reubenwbetts/Digitally-Controlled-Analog-EQ/Digital-Control/Digipot-Board/PCB-Layouts/Layer 1 (top).png

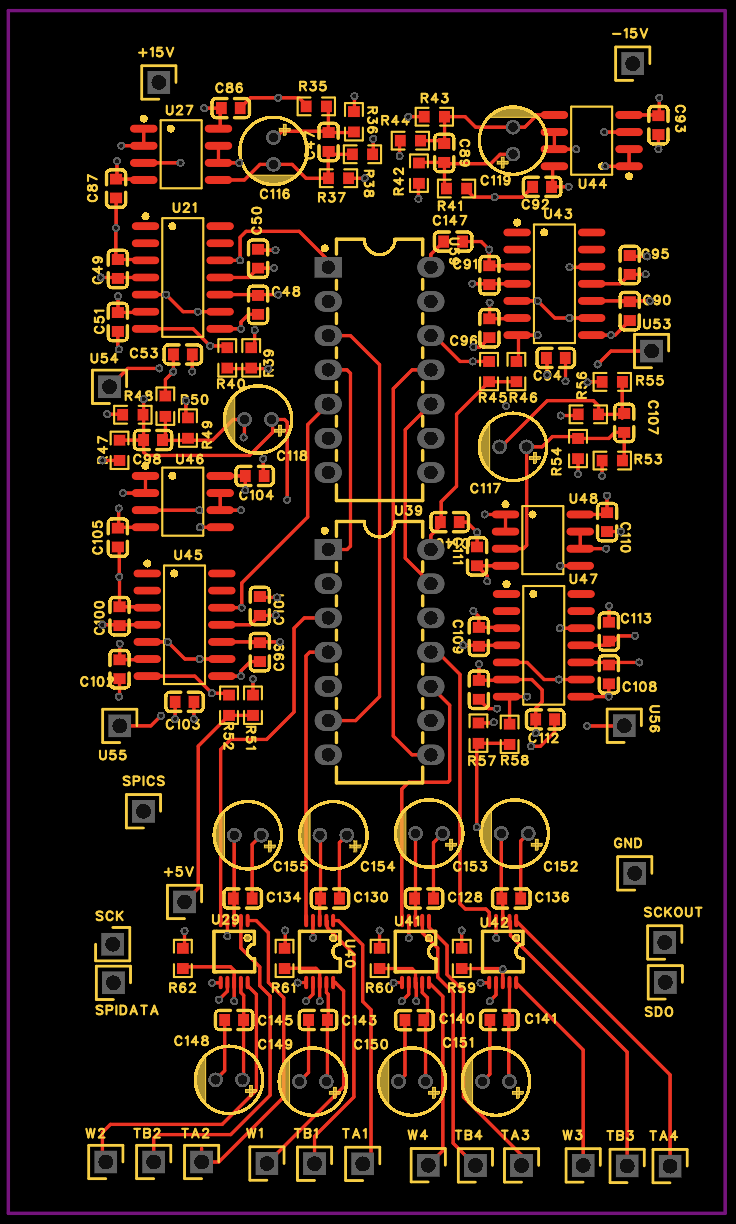
Digital-Control/Digipot-Board/PCB-Layouts/Layer 1 (top).png
