reubenwbetts/Digitally-Controlled-Analog-EQ/Digital-Control/Digipot-Board/PCB-Layouts/Layer 2.png

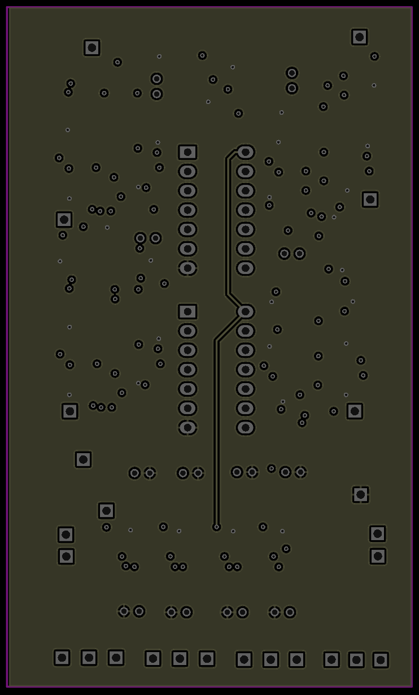
Digital-Control/Digipot-Board/PCB-Layouts/Layer 2.png
