reubenwbetts/Digitally-Controlled-Analog-EQ/Digital-Control/Digipot-Board/PCB-Layouts/Layer 3.png

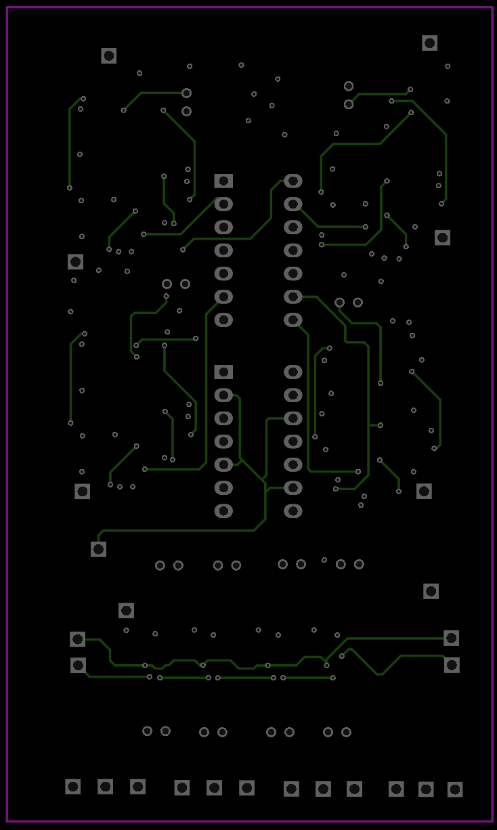
Digital-Control/Digipot-Board/PCB-Layouts/Layer 3.png
