reubenwbetts/Digitally-Controlled-Analog-EQ/Digital-Control/Digipot-Board/PCB-Layouts/Layer 4 (bottom).png

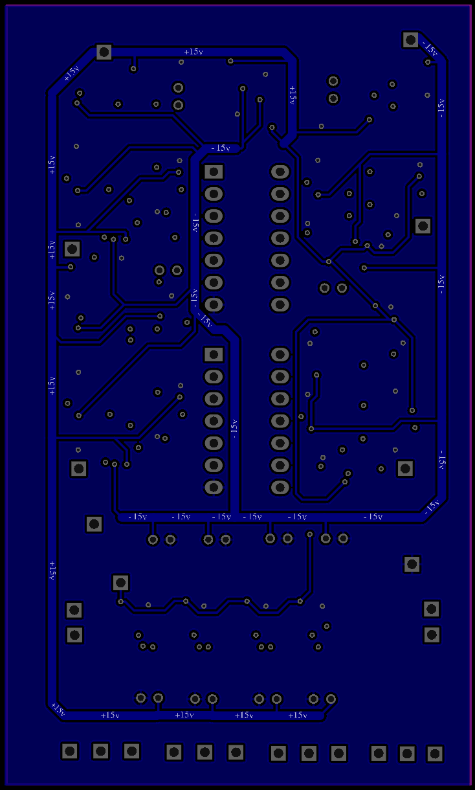
Digital-Control/Digipot-Board/PCB-Layouts/Layer 4 (bottom).png
