reubenwbetts/Digitally-Controlled-Analog-EQ/EQ-Channel/PCB-files/Bottom Layer.png

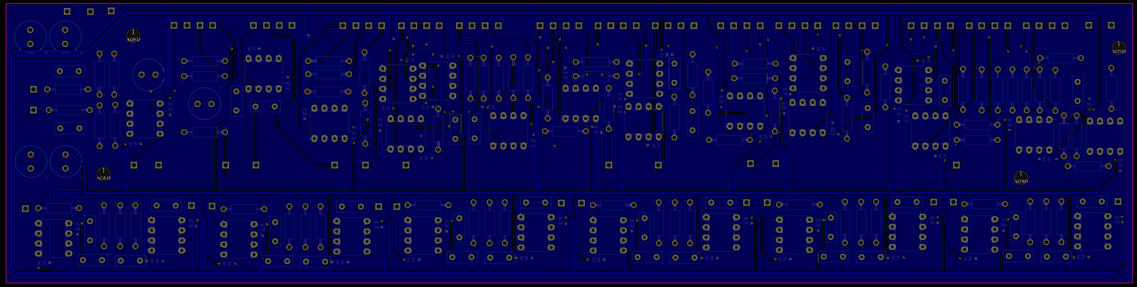
EQ-Channel/PCB-files/Bottom Layer.png
