reubenwbetts/Digitally-Controlled-Analog-EQ/EQ-Channel/PCB-files/Top Layer.png

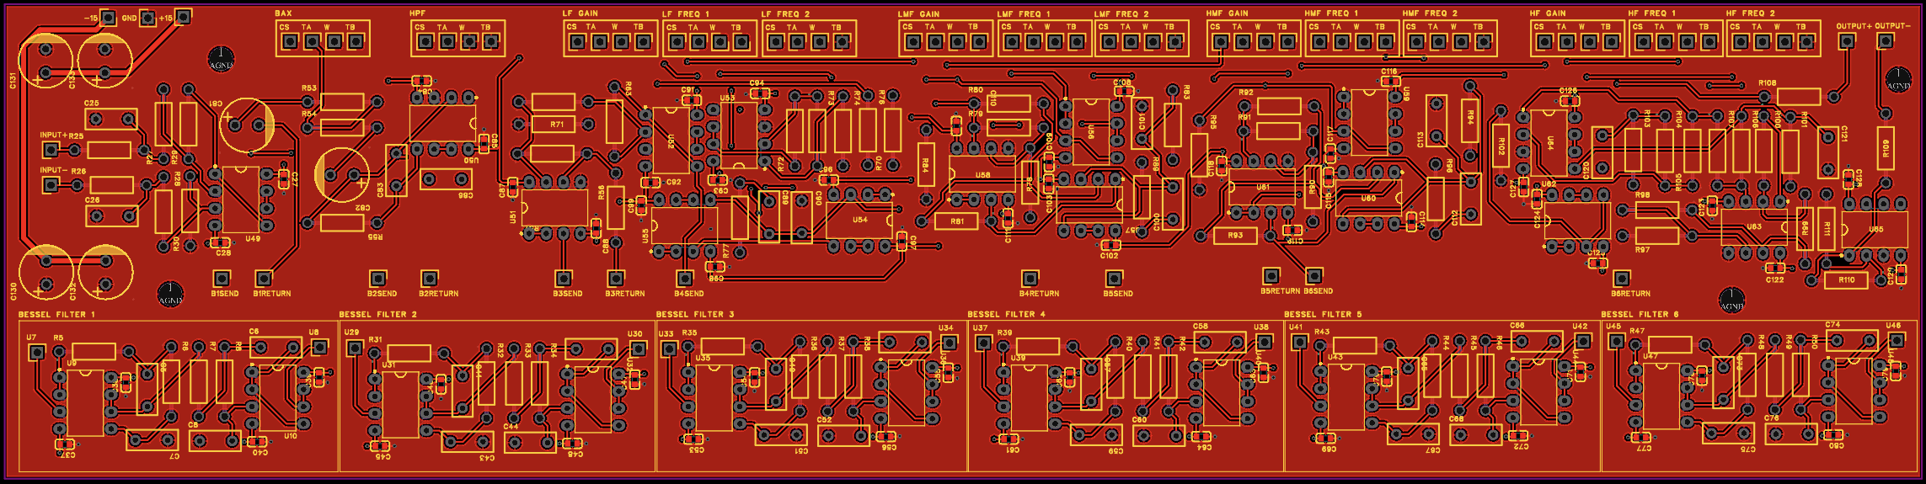
EQ-Channel/PCB-files/Top Layer.png
