reubenwbetts/Digitally-Controlled-Analog-EQ/EQ-Channel/Schematics/Balanced Input.png

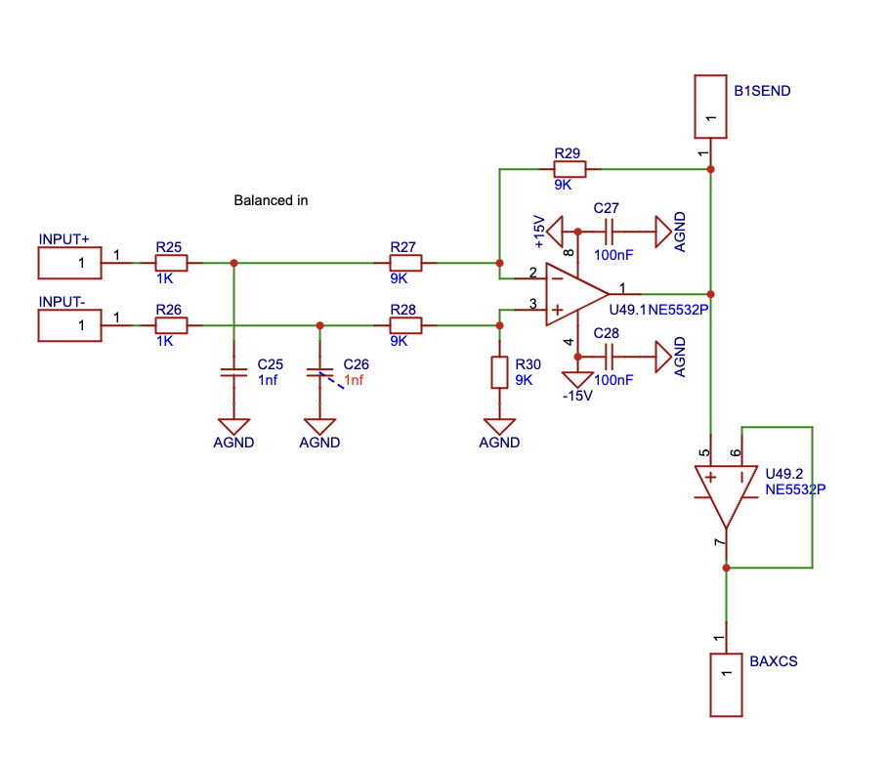
EQ-Channel/Schematics/Balanced Input.png
