reubenwbetts/Digitally-Controlled-Analog-EQ/EQ-Channel/Schematics/Low Mid Bell.png

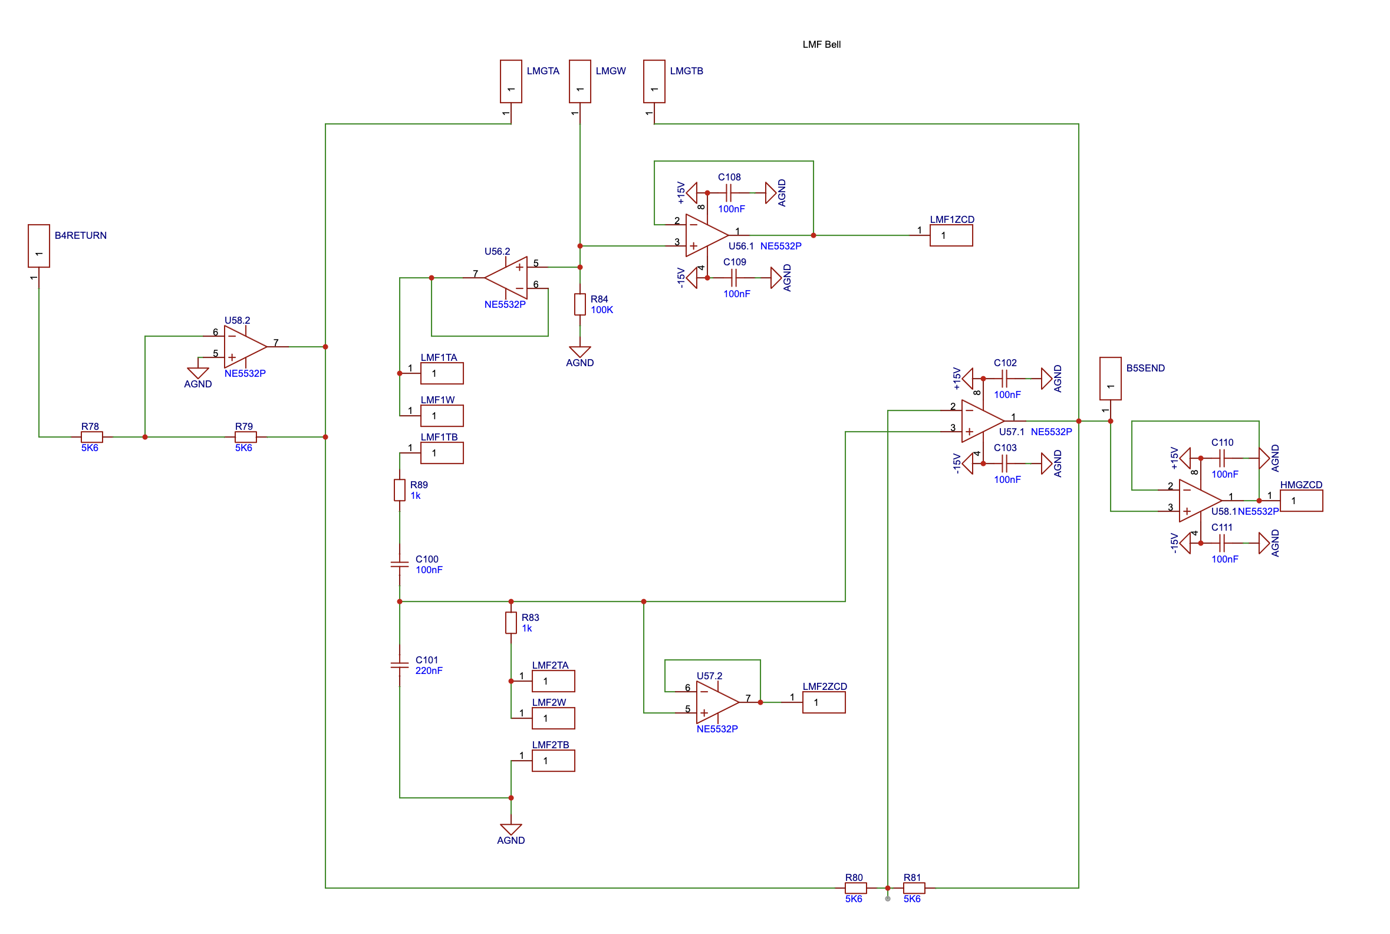
EQ-Channel/Schematics/Low Mid Bell.png
