reubenwbetts/Digitally-Controlled-Analog-EQ/EQ-Channel/Spice-Sims/Balanced Input.asc

C1: cap; 1nf
C2: cap; 1nf
R1: res; 9K
R2: res; 9K
R3: res; 9K
R4: res; 9K
R5: res; 1K
R6: res; 1K
U1: opamp2; NE5532
V1: voltage; 15
V2: voltage; -15
V3: voltage; SINE(0 1 100); AC 1
V4: voltage; SINE(0 1 100 0 0 180); AC 1 180
Named nets: +15, -15, 0, sig-, sig+
.lib LTC.lib
.ac oct 100 1 100k
.tran 0.1
