reubenwbetts/Digitally-Controlled-Analog-EQ/Digital-Control/Bessel-Filter/Spice-Sims/Bessel Filter.asc

0.7381nf: cap; 0.7381nf
C1: cap; 12.0839nf
C2: cap; 9.0713nf
C3: cap; 33nf
C4: cap; 1.5879nf
C5: cap; 0.3791nf
C6: cap; 24nf
C7: cap; 1.3917nf
C8: cap; 0.9403nf
C9: cap; 0.9403nf
C10: cap; 0.7157nf
C11: cap; 1.2772nf
C12: cap; 1.9158nf
C13: cap; 0.9027nf
C14: cap; 0.7157nf
C15: cap; 0.9027nf
C16: cap; 1.0694nf
C17: cap; 720pf
C18: cap; 10pf
C19: cap; 68pf
C20: cap; 540pf
C21: cap; 15pf
C22: cap; 720pf
C23: cap; 10pf
C24: cap; 68pf
C25: cap; 540pf
C26: cap; 15pf
C27: cap; 1.0694nf
C28: cap; 1.5879nf
C29: cap; 0.3791nf
C30: cap; 1.3917nf
C31: cap; 0.7381nf
C32: cap; 1.2772nf
C33: cap; 1.9158nf
R1: res; 220
R2: res; 220
R3: res; 1k
R4: res; 1k
R5: res; 1k
R6: res; 1k
R7: res; 1k
R8: res; 1k
R9: res; 1k
R10: res; 1k
R11: res; 1k
R12: res; 1k
R13: res; 10k
R14: res; 10k
R15: res; 10k
R16: res; 10k
R17: res; 10k
R18: res; 10k
R19: res; 10k
R20: res; 10k
R21: res; 100
R22: res; 100
R23: res; 1k
R24: res; 1k
R25: res; 1k
R26: res; 1k
R27: res; 1k
R28: res; 1k
R29: res; 1k
R30: res; 1k
R31: res; 1k
R32: res; 1k
U1: opamp2; NE5532
U2: opamp2; NE5532
U3: opamp2; NE5532
U4: opamp2; NE5532
U5: opamp2; NE5532
U6: opamp2; NE5532
U7: opamp2; NE5532
U8: opamp2; NE5532
U9: opamp2; NE5532
U10: opamp2; NE5532
U11: opamp2; NE5532
U12: opamp2; NE5532
U13: opamp2; NE5532
U14: opamp2; NE5532
U15: opamp2; NE5532
U16: opamp2; NE5532
V1: voltage; +15
V2: voltage; -15
V3: voltage; SINE(0 1 {sigfreq}); AC 1
Named nets: 0, +15, -15, sig, 6order, 2order, 2ordernewcalc
.lib LTC.lib
.ac oct 100 1 200k
.tran 0 0.0001
2nd Order
voltage sources
simulation directives:
.lib LTC.lib
4th Order
.lib LTC.lib
6th Order
.lib LTC.lib
8th Order
.lib LTC.lib
Components values determined by BesselFilterCalc.m
.lib LTC.lib
2nd Order
.lib LTC.lib
6th Order
.lib LTC.lib
4th Order
.tran to check delay times
.ac to check frequency response and phase linearity
.step param sigfreq list 100 1k 10k 20k
.param sigfreq = 10k
